PhilKes/HomePlantery/3dprint/watering_system/4mm_Sprinkler_Top_vertical_4way.stl

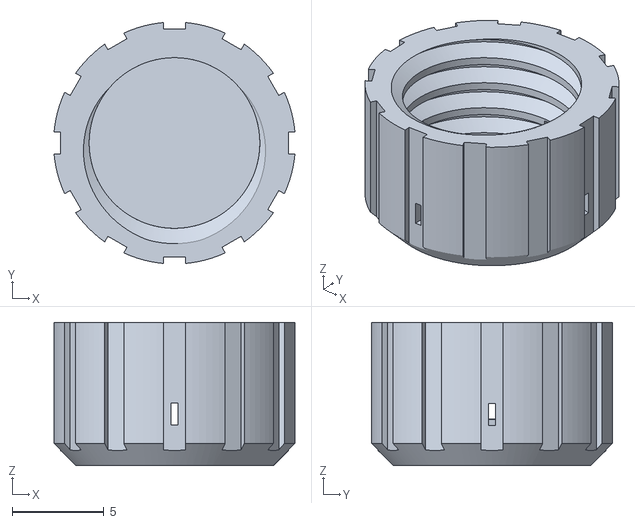
[picture p17: CAD file, 2024-07-07]
3dprint/watering_system/4mm_Sprinkler_Top_vertical_4way.stl
13.1 x 13.1 x 7.80
