PhilKes/HomePlantery/3dprint/watering_system/8-to-4mm-7-way-Splitter.stl

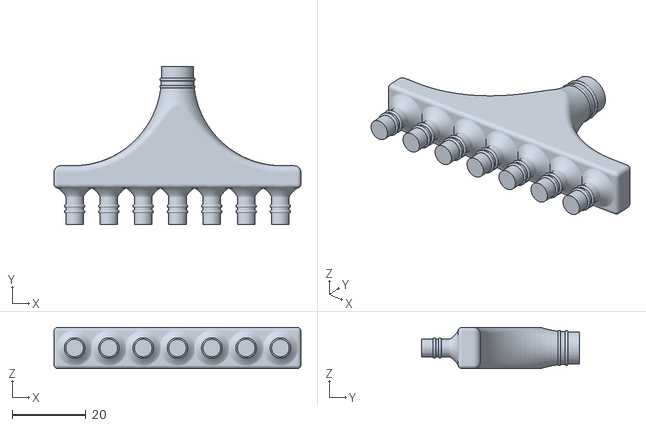
[picture p18: CAD file, 2024-07-07]
3dprint/watering_system/8-to-4mm-7-way-Splitter.stl
67.2 x 43.0 x 11.2
