PhilKes/HomePlantery/3dprint/watering_system/4mm_Sprinkler_Top_vertical.stl

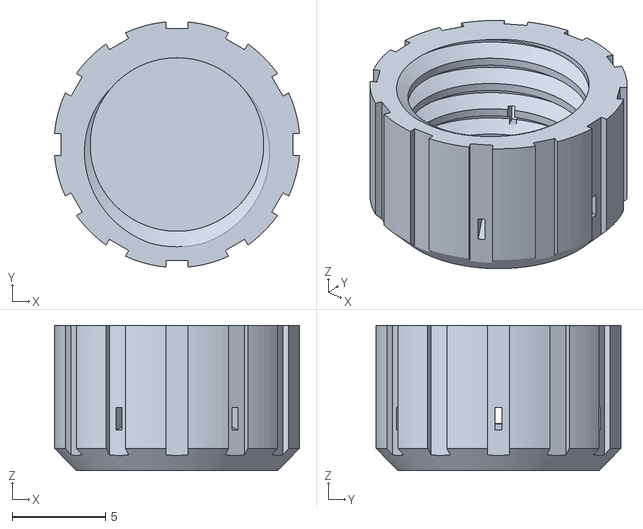
[picture p19: CAD file, 2024-07-07]
3dprint/watering_system/4mm_Sprinkler_Top_vertical.stl
13.1 x 13.1 x 7.80
