PhilKes/HomePlantery/3dprint/watering_system/4mm_Sprinkler_Top_Big.stl

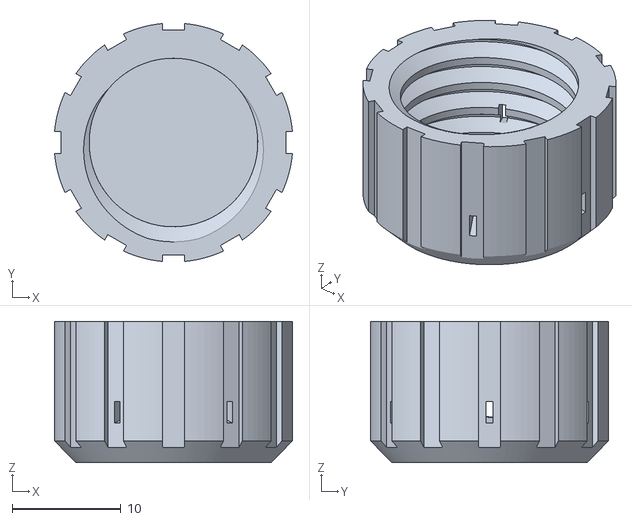
[picture p20: CAD file, 2024-07-07]
3dprint/watering_system/4mm_Sprinkler_Top_Big.stl
21.9 x 21.9 x 13.0
