PhilKes/HomePlantery/3dprint/watering_system/4mm_Sprinkler_bottom_small.stl

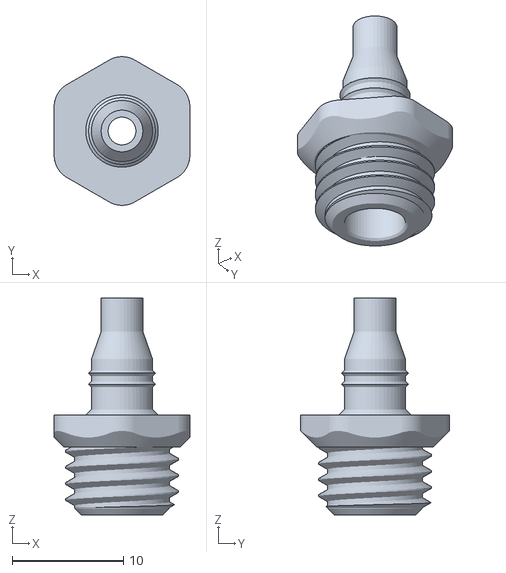
[picture p21: CAD file, 2024-07-07]
3dprint/watering_system/4mm_Sprinkler_bottom_small.stl
12.2 x 13.4 x 19.5
