PhilKes/HomePlantery/3dprint/watering_system/4mm_Tube_3_way_connector.stl

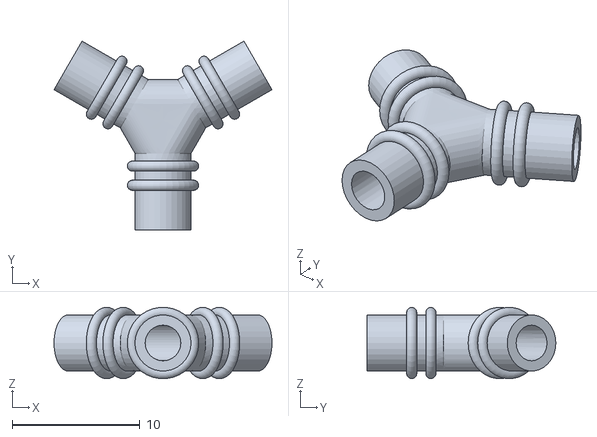
[picture p22: CAD file, 2024-07-07]
3dprint/watering_system/4mm_Tube_3_way_connector.stl
17.1 x 14.8 x 5.58
