PhilKes/HomePlantery/3dprint/watering_system/8-to-4mm-5-way-Splitter.stl

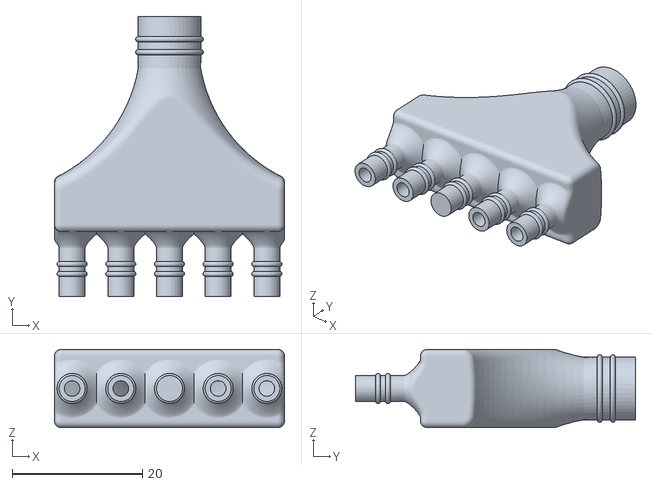
[picture p23: CAD file, 2024-07-07]
3dprint/watering_system/8-to-4mm-5-way-Splitter.stl
35.3 x 43.0 x 12.0
