PhilKes/HomePlantery/3dprint/watering_system/splitter_small_test.stl

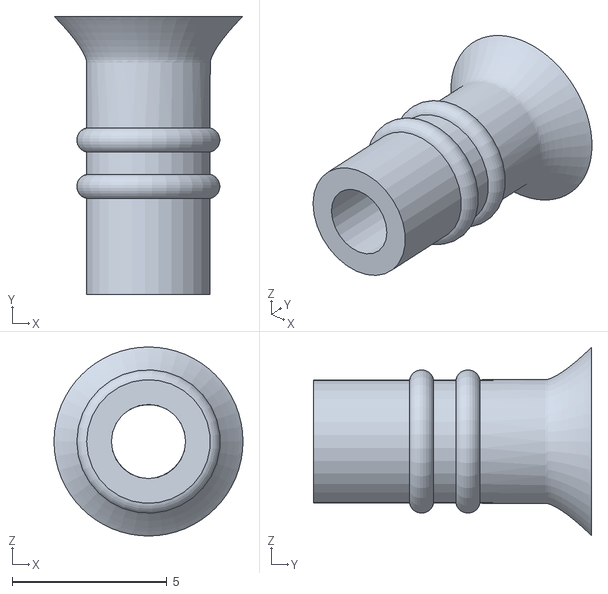
[picture p24: CAD file, 2024-07-07]
3dprint/watering_system/splitter_small_test.stl
6.11 x 9.00 x 6.11
